738NGX/RinaChanBoard/Documents/Assets/头图.png

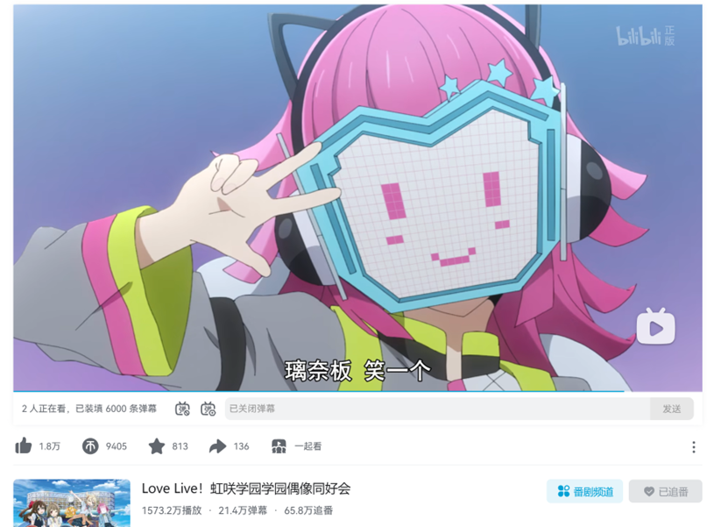
Documents/Assets/头图.png
