738NGX/RinaChanBoard/RinaChanBoardHardware/PCB/RinaBoard/resources/rina2.png

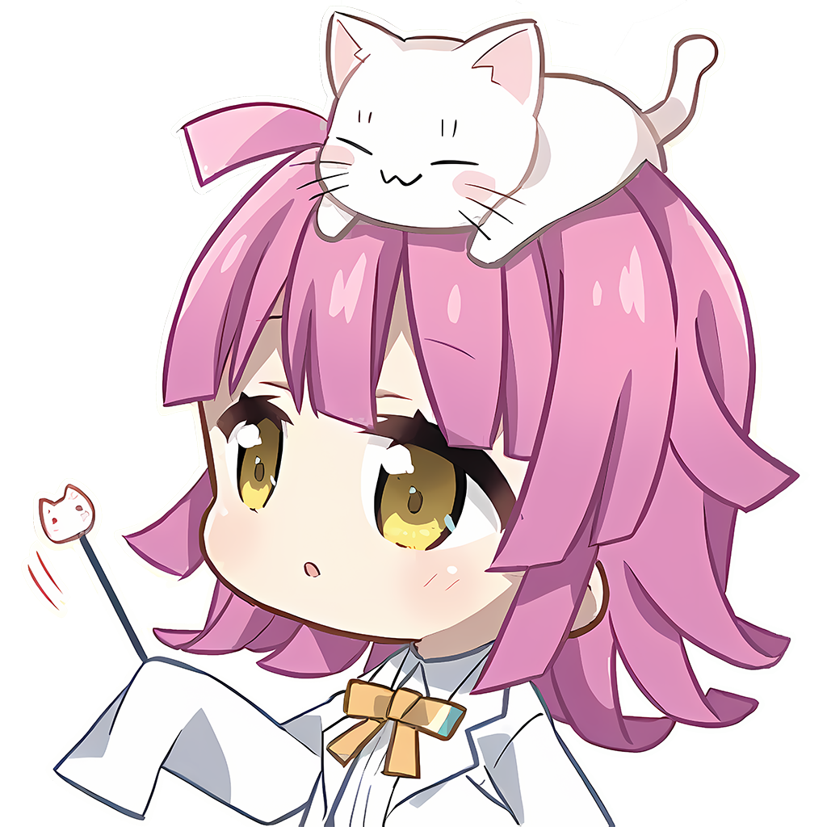
RinaChanBoardHardware/PCB/RinaBoard/resources/rina2.png
