738NGX/RinaChanBoard/RinaChanBoardHardware/PCB/RinaBoard/resources/rina3.png

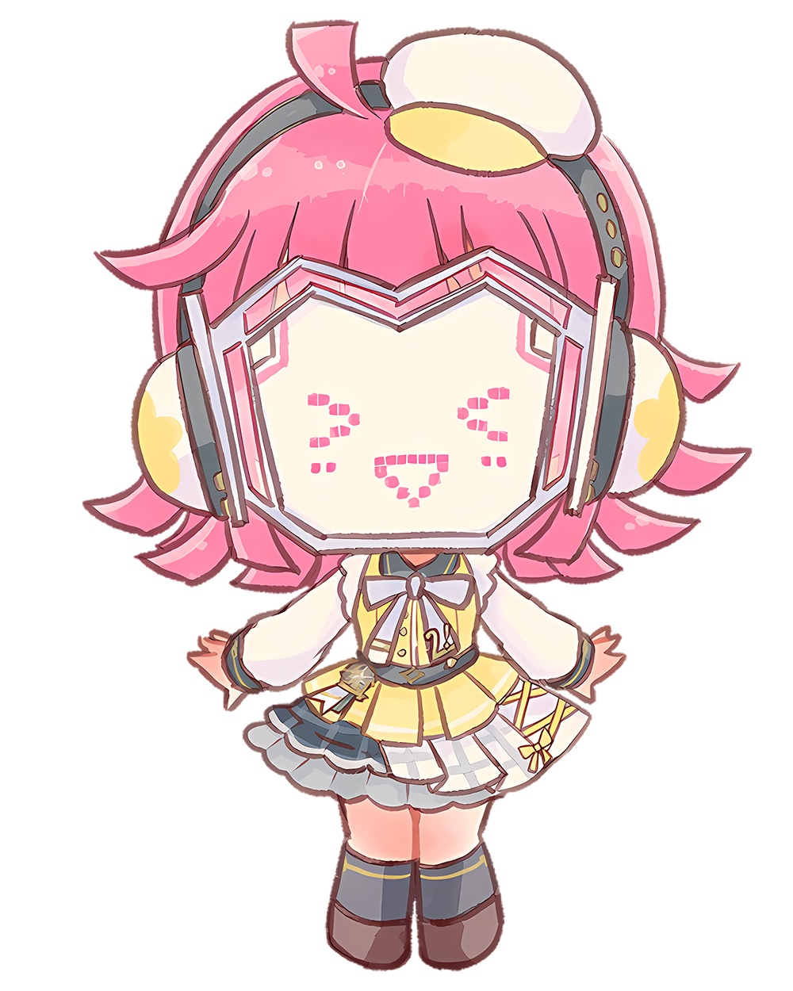
RinaChanBoardHardware/PCB/RinaBoard/resources/rina3.png
