738NGX/RinaChanBoard/RinaChanBoardHardware/PCB/RinaBoard/resources/rina.png

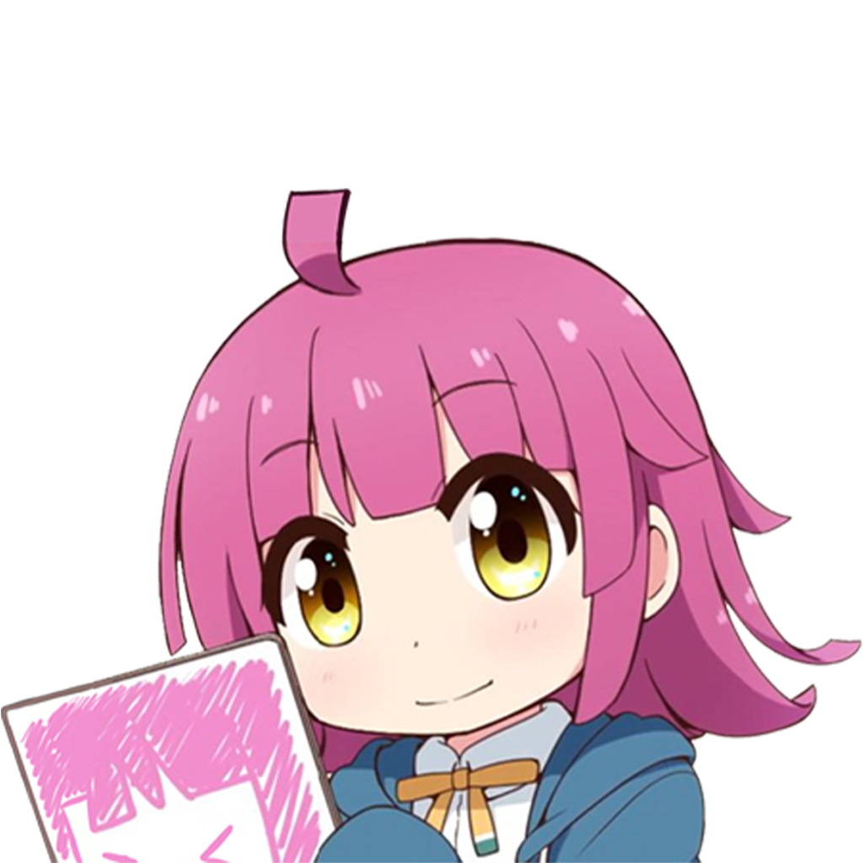
RinaChanBoardHardware/PCB/RinaBoard/resources/rina.png
