738NGX/RinaChanBoard/RinaChanBoardOperationCenter.wechatapp/images/cheek/01.png

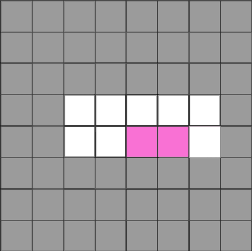
RinaChanBoardOperationCenter.wechatapp/images/cheek/01.png
