738NGX/RinaChanBoard/RinaChanBoardOperationCenter.wechatapp/images/cheek/03.png

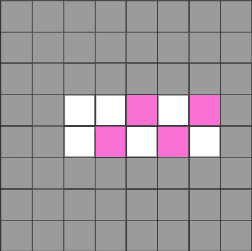
RinaChanBoardOperationCenter.wechatapp/images/cheek/03.png
