738NGX/RinaChanBoard/RinaChanBoardOperationCenter.wechatapp/images/cheek/04.png

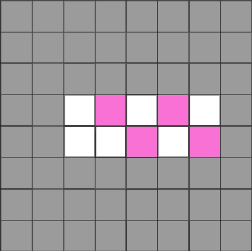
RinaChanBoardOperationCenter.wechatapp/images/cheek/04.png
