738NGX/RinaChanBoard/RinaChanBoardOperationCenter.wechatapp/images/connected.png

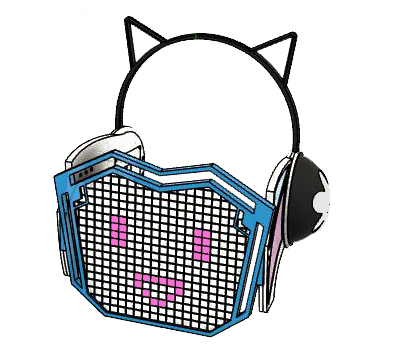
RinaChanBoardOperationCenter.wechatapp/images/connected.png
