738NGX/RinaChanBoard/RinaChanBoardOperationCenter.wechatapp/images/disconnected.png

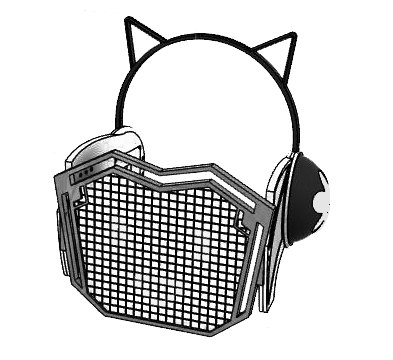
RinaChanBoardOperationCenter.wechatapp/images/disconnected.png
