738NGX/RinaChanBoard/RinaChanBoardOperationCenter.wechatapp/images/leye/05.png

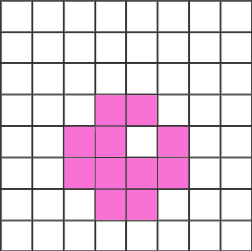
RinaChanBoardOperationCenter.wechatapp/images/leye/05.png
