738NGX/RinaChanBoard/RinaChanBoardOperationCenter.wechatapp/images/leye/09.png

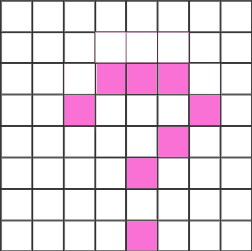
RinaChanBoardOperationCenter.wechatapp/images/leye/09.png
