738NGX/RinaChanBoard/RinaChanBoardOperationCenter.wechatapp/images/leye/18.png

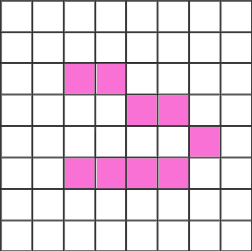
RinaChanBoardOperationCenter.wechatapp/images/leye/18.png
