738NGX/RinaChanBoard/RinaChanBoardOperationCenter.wechatapp/images/play.png

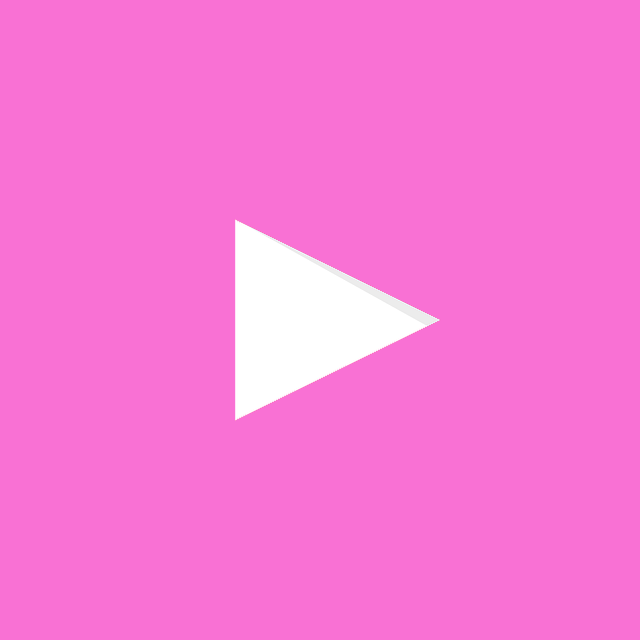
RinaChanBoardOperationCenter.wechatapp/images/play.png
