738NGX/RinaChanBoard/RinaChanBoardOperationCenter.wechatapp/images/reye/18.png

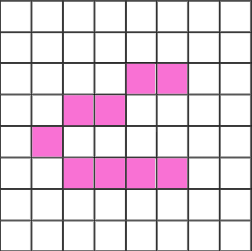
RinaChanBoardOperationCenter.wechatapp/images/reye/18.png
