738NGX/RinaChanBoard/RinaChanBoardOperationCenter/Assets/Resources/Image/FaceModule/000.png

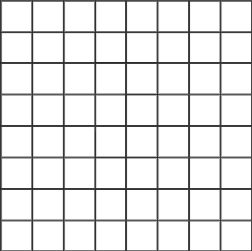
RinaChanBoardOperationCenter/Assets/Resources/Image/FaceModule/000.png
