738NGX/RinaChanBoard/RinaChanBoardOperationCenter/Assets/Resources/Image/FaceModule/101.png

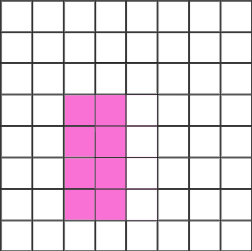
RinaChanBoardOperationCenter/Assets/Resources/Image/FaceModule/101.png
