738NGX/RinaChanBoard/RinaChanBoardOperationCenter/Assets/Resources/Image/FaceModule/103.png

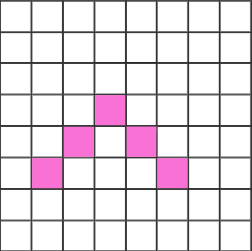
RinaChanBoardOperationCenter/Assets/Resources/Image/FaceModule/103.png
