738NGX/RinaChanBoard/RinaChanBoardOperationCenter/Assets/Resources/Image/FaceModule/104.png

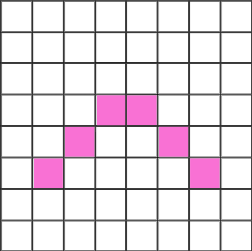
RinaChanBoardOperationCenter/Assets/Resources/Image/FaceModule/104.png
