738NGX/RinaChanBoard/RinaChanBoardOperationCenter/Assets/Resources/Image/FaceModule/105.png

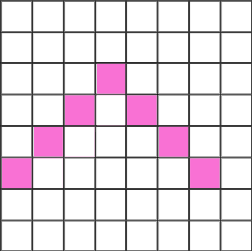
RinaChanBoardOperationCenter/Assets/Resources/Image/FaceModule/105.png
