738NGX/RinaChanBoard/RinaChanBoardOperationCenter/Assets/Resources/Image/FaceModule/106.png

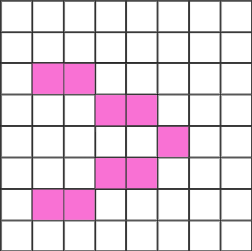
RinaChanBoardOperationCenter/Assets/Resources/Image/FaceModule/106.png
