738NGX/RinaChanBoard/RinaChanBoardOperationCenter/Assets/Resources/Image/FaceModule/107.png

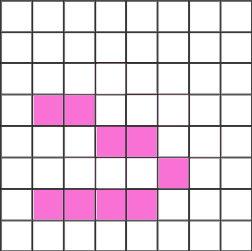
RinaChanBoardOperationCenter/Assets/Resources/Image/FaceModule/107.png
