738NGX/RinaChanBoard/RinaChanBoardOperationCenter/Assets/Resources/Image/FaceModule/109.png

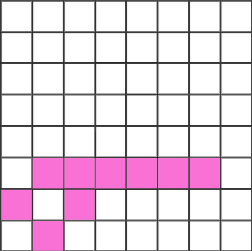
RinaChanBoardOperationCenter/Assets/Resources/Image/FaceModule/109.png
