738NGX/RinaChanBoard/RinaChanBoardOperationCenter/Assets/Resources/Image/FaceModule/110.png

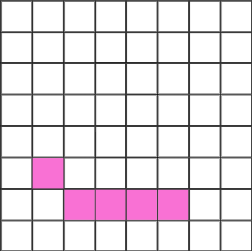
RinaChanBoardOperationCenter/Assets/Resources/Image/FaceModule/110.png
