738NGX/RinaChanBoard/RinaChanBoardOperationCenter/Assets/Resources/Image/FaceModule/111.png

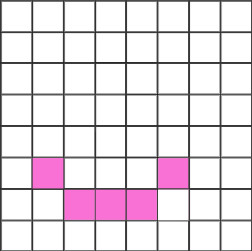
RinaChanBoardOperationCenter/Assets/Resources/Image/FaceModule/111.png
