738NGX/RinaChanBoard/RinaChanBoardOperationCenter/Assets/Resources/Image/FaceModule/112.png

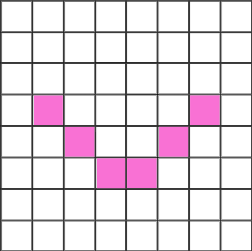
RinaChanBoardOperationCenter/Assets/Resources/Image/FaceModule/112.png
