738NGX/RinaChanBoard/RinaChanBoardOperationCenter/Assets/Resources/Image/FaceModule/113.png

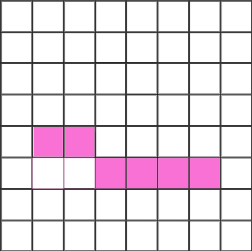
RinaChanBoardOperationCenter/Assets/Resources/Image/FaceModule/113.png
