738NGX/RinaChanBoard/RinaChanBoardOperationCenter/Assets/Resources/Image/FaceModule/117.png

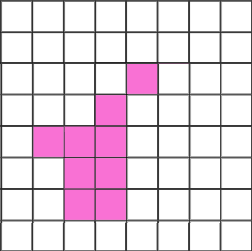
RinaChanBoardOperationCenter/Assets/Resources/Image/FaceModule/117.png
