738NGX/RinaChanBoard/RinaChanBoardOperationCenter/Assets/Resources/Image/FaceModule/118.png

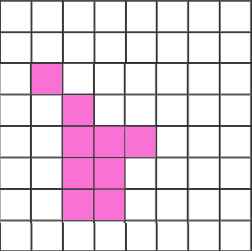
RinaChanBoardOperationCenter/Assets/Resources/Image/FaceModule/118.png
