738NGX/RinaChanBoard/RinaChanBoardOperationCenter/Assets/Resources/Image/FaceModule/119.png

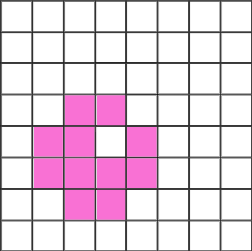
RinaChanBoardOperationCenter/Assets/Resources/Image/FaceModule/119.png
