738NGX/RinaChanBoard/RinaChanBoardOperationCenter/Assets/Resources/Image/FaceModule/122.png

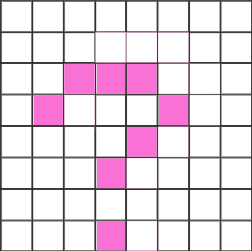
RinaChanBoardOperationCenter/Assets/Resources/Image/FaceModule/122.png
