738NGX/RinaChanBoard/RinaChanBoardOperationCenter/Assets/Resources/Image/FaceModule/123.png

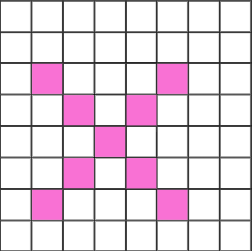
RinaChanBoardOperationCenter/Assets/Resources/Image/FaceModule/123.png
