738NGX/RinaChanBoard/RinaChanBoardOperationCenter/Assets/Resources/Image/FaceModule/124.png

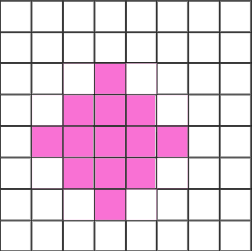
RinaChanBoardOperationCenter/Assets/Resources/Image/FaceModule/124.png
