738NGX/RinaChanBoard/RinaChanBoardOperationCenter/Assets/Resources/Image/FaceModule/125.png

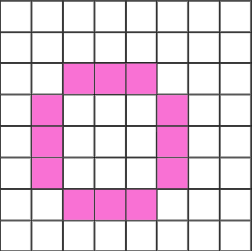
RinaChanBoardOperationCenter/Assets/Resources/Image/FaceModule/125.png
