738NGX/RinaChanBoard/RinaChanBoardOperationCenter/Assets/Resources/Image/FaceModule/126.png

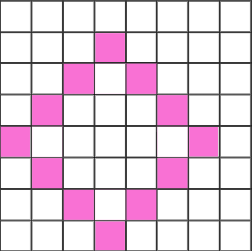
RinaChanBoardOperationCenter/Assets/Resources/Image/FaceModule/126.png
