738NGX/RinaChanBoard/RinaChanBoardOperationCenter/Assets/Resources/Image/FaceModule/127.png

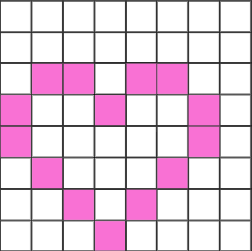
RinaChanBoardOperationCenter/Assets/Resources/Image/FaceModule/127.png
