738NGX/RinaChanBoard/RinaChanBoardOperationCenter/Assets/Resources/Image/FaceModule/201.png

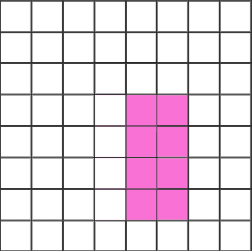
RinaChanBoardOperationCenter/Assets/Resources/Image/FaceModule/201.png
