738NGX/RinaChanBoard/RinaChanBoardOperationCenter/Assets/Resources/Image/FaceModule/203.png

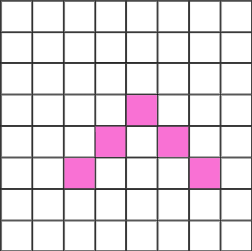
RinaChanBoardOperationCenter/Assets/Resources/Image/FaceModule/203.png
