738NGX/RinaChanBoard/RinaChanBoardOperationCenter/Assets/Resources/Image/FaceModule/205.png

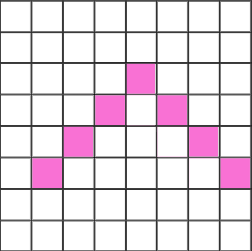
RinaChanBoardOperationCenter/Assets/Resources/Image/FaceModule/205.png
