738NGX/RinaChanBoard/RinaChanBoardOperationCenter/Assets/Resources/Image/FaceModule/206.png

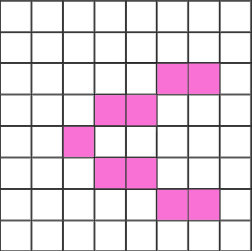
RinaChanBoardOperationCenter/Assets/Resources/Image/FaceModule/206.png
