738NGX/RinaChanBoard/RinaChanBoardOperationCenter/Assets/Resources/Image/FaceModule/207.png

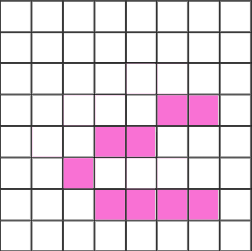
RinaChanBoardOperationCenter/Assets/Resources/Image/FaceModule/207.png
