738NGX/RinaChanBoard/RinaChanBoardOperationCenter/Assets/Resources/Image/FaceModule/209.png

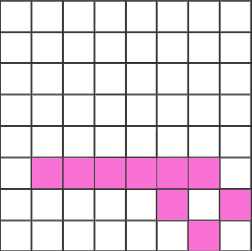
RinaChanBoardOperationCenter/Assets/Resources/Image/FaceModule/209.png
