738NGX/RinaChanBoard/RinaChanBoardOperationCenter/Assets/Resources/Image/FaceModule/210.png

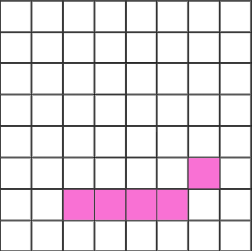
RinaChanBoardOperationCenter/Assets/Resources/Image/FaceModule/210.png
