738NGX/RinaChanBoard/RinaChanBoardOperationCenter/Assets/Resources/Image/FaceModule/211.png

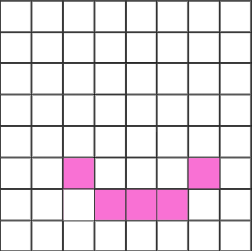
RinaChanBoardOperationCenter/Assets/Resources/Image/FaceModule/211.png
