738NGX/RinaChanBoard/RinaChanBoardOperationCenter/Assets/Resources/Image/FaceModule/213.png

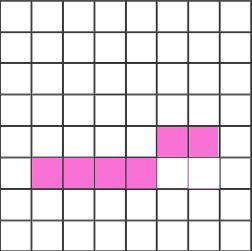
RinaChanBoardOperationCenter/Assets/Resources/Image/FaceModule/213.png
