738NGX/RinaChanBoard/RinaChanBoardOperationCenter/Assets/Resources/Image/FaceModule/214.png

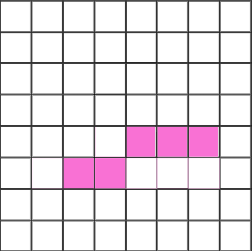
RinaChanBoardOperationCenter/Assets/Resources/Image/FaceModule/214.png
