738NGX/RinaChanBoard/RinaChanBoardOperationCenter/Assets/Resources/Image/FaceModule/216.png

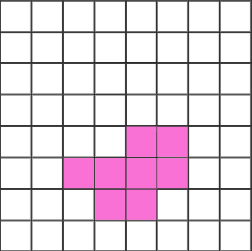
RinaChanBoardOperationCenter/Assets/Resources/Image/FaceModule/216.png
