738NGX/RinaChanBoard/RinaChanBoardOperationCenter/Assets/Resources/Image/FaceModule/217.png

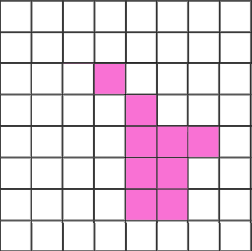
RinaChanBoardOperationCenter/Assets/Resources/Image/FaceModule/217.png
