738NGX/RinaChanBoard/RinaChanBoardOperationCenter/Assets/Resources/Image/FaceModule/218.png

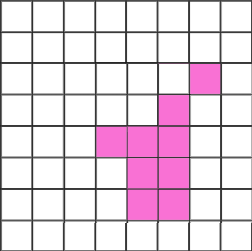
RinaChanBoardOperationCenter/Assets/Resources/Image/FaceModule/218.png
