738NGX/RinaChanBoard/RinaChanBoardOperationCenter/Assets/Resources/Image/FaceModule/219.png

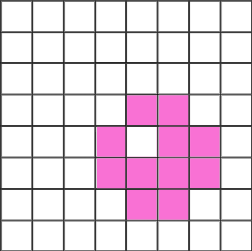
RinaChanBoardOperationCenter/Assets/Resources/Image/FaceModule/219.png
