738NGX/RinaChanBoard/RinaChanBoardOperationCenter/Assets/Resources/Image/FaceModule/222.png

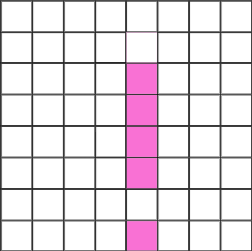
RinaChanBoardOperationCenter/Assets/Resources/Image/FaceModule/222.png
