738NGX/RinaChanBoard/RinaChanBoardOperationCenter/Assets/Resources/Image/FaceModule/223.png

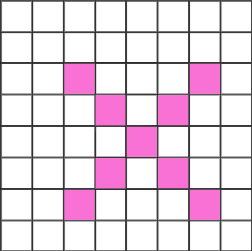
RinaChanBoardOperationCenter/Assets/Resources/Image/FaceModule/223.png
