738NGX/RinaChanBoard/RinaChanBoardOperationCenter/Assets/Resources/Image/FaceModule/224.png

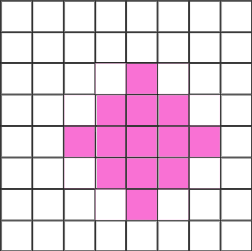
RinaChanBoardOperationCenter/Assets/Resources/Image/FaceModule/224.png
