738NGX/RinaChanBoard/RinaChanBoardOperationCenter/Assets/Resources/Image/FaceModule/225.png

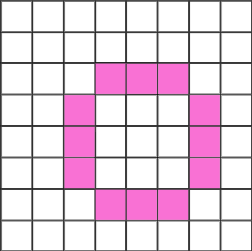
RinaChanBoardOperationCenter/Assets/Resources/Image/FaceModule/225.png
