738NGX/RinaChanBoard/RinaChanBoardOperationCenter/Assets/Resources/Image/FaceModule/226.png

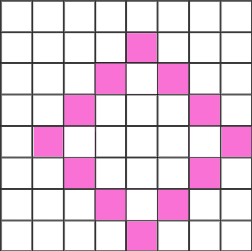
RinaChanBoardOperationCenter/Assets/Resources/Image/FaceModule/226.png
