738NGX/RinaChanBoard/RinaChanBoardOperationCenter/Assets/Resources/Image/FaceModule/227.png

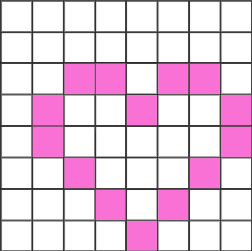
RinaChanBoardOperationCenter/Assets/Resources/Image/FaceModule/227.png
