738NGX/RinaChanBoard/RinaChanBoardOperationCenter/Assets/Resources/Image/FaceModule/302.png

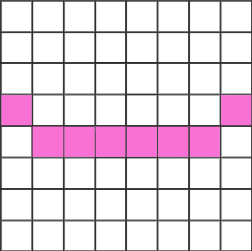
RinaChanBoardOperationCenter/Assets/Resources/Image/FaceModule/302.png
