738NGX/RinaChanBoard/RinaChanBoardOperationCenter/Assets/Resources/Image/FaceModule/303.png

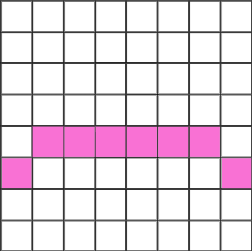
RinaChanBoardOperationCenter/Assets/Resources/Image/FaceModule/303.png
