738NGX/RinaChanBoard/RinaChanBoardOperationCenter/Assets/Resources/Image/FaceModule/304.png

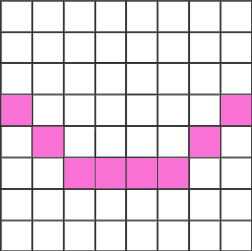
RinaChanBoardOperationCenter/Assets/Resources/Image/FaceModule/304.png
