738NGX/RinaChanBoard/RinaChanBoardOperationCenter/Assets/Resources/Image/FaceModule/305.png

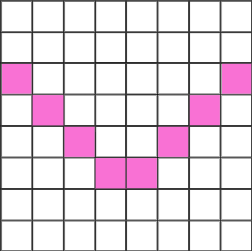
RinaChanBoardOperationCenter/Assets/Resources/Image/FaceModule/305.png
