738NGX/RinaChanBoard/RinaChanBoardOperationCenter/Assets/Resources/Image/FaceModule/307.png

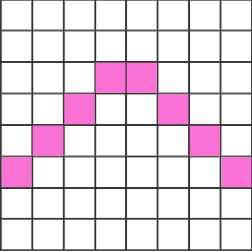
RinaChanBoardOperationCenter/Assets/Resources/Image/FaceModule/307.png
