738NGX/RinaChanBoard/RinaChanBoardOperationCenter/Assets/Resources/Image/FaceModule/308.png

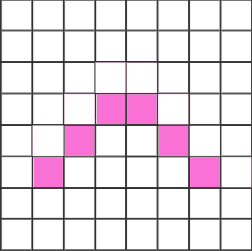
RinaChanBoardOperationCenter/Assets/Resources/Image/FaceModule/308.png
