738NGX/RinaChanBoard/RinaChanBoardOperationCenter/Assets/Resources/Image/FaceModule/309.png

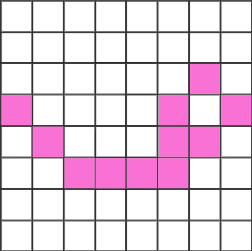
RinaChanBoardOperationCenter/Assets/Resources/Image/FaceModule/309.png
