738NGX/RinaChanBoard/RinaChanBoardOperationCenter/Assets/Resources/Image/FaceModule/310.png

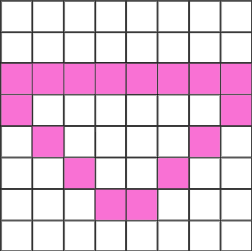
RinaChanBoardOperationCenter/Assets/Resources/Image/FaceModule/310.png
