738NGX/RinaChanBoard/RinaChanBoardOperationCenter/Assets/Resources/Image/FaceModule/311.png

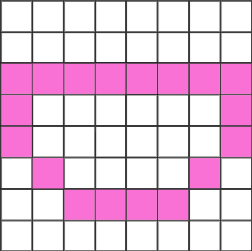
RinaChanBoardOperationCenter/Assets/Resources/Image/FaceModule/311.png
