738NGX/RinaChanBoard/RinaChanBoardOperationCenter/Assets/Resources/Image/FaceModule/312.png

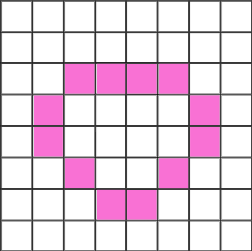
RinaChanBoardOperationCenter/Assets/Resources/Image/FaceModule/312.png
