738NGX/RinaChanBoard/RinaChanBoardOperationCenter/Assets/Resources/Image/FaceModule/314.png

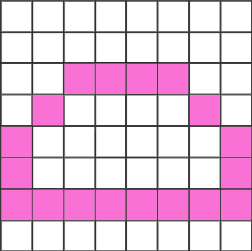
RinaChanBoardOperationCenter/Assets/Resources/Image/FaceModule/314.png
