738NGX/RinaChanBoard/RinaChanBoardOperationCenter/Assets/Resources/Image/FaceModule/315.png

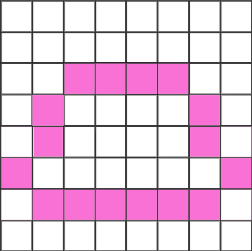
RinaChanBoardOperationCenter/Assets/Resources/Image/FaceModule/315.png
