738NGX/RinaChanBoard/RinaChanBoardOperationCenter/Assets/Resources/Image/FaceModule/316.png

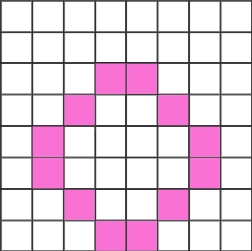
RinaChanBoardOperationCenter/Assets/Resources/Image/FaceModule/316.png
