738NGX/RinaChanBoard/RinaChanBoardOperationCenter/Assets/Resources/Image/FaceModule/317.png

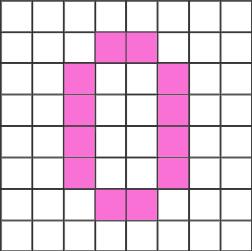
RinaChanBoardOperationCenter/Assets/Resources/Image/FaceModule/317.png
