738NGX/RinaChanBoard/RinaChanBoardOperationCenter/Assets/Resources/Image/FaceModule/318.png

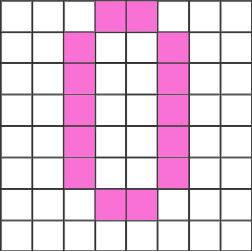
RinaChanBoardOperationCenter/Assets/Resources/Image/FaceModule/318.png
