738NGX/RinaChanBoard/RinaChanBoardOperationCenter/Assets/Resources/Image/FaceModule/319.png

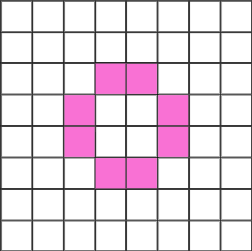
RinaChanBoardOperationCenter/Assets/Resources/Image/FaceModule/319.png
