738NGX/RinaChanBoard/RinaChanBoardOperationCenter/Assets/Resources/Image/FaceModule/320.png

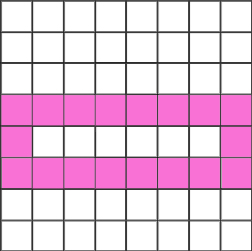
RinaChanBoardOperationCenter/Assets/Resources/Image/FaceModule/320.png
