738NGX/RinaChanBoard/RinaChanBoardOperationCenter/Assets/Resources/Image/FaceModule/323.png

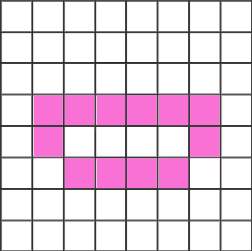
RinaChanBoardOperationCenter/Assets/Resources/Image/FaceModule/323.png
