738NGX/RinaChanBoard/RinaChanBoardOperationCenter/Assets/Resources/Image/FaceModule/324.png

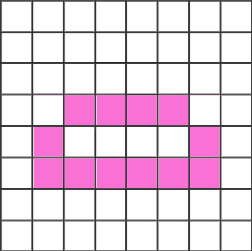
RinaChanBoardOperationCenter/Assets/Resources/Image/FaceModule/324.png
