738NGX/RinaChanBoard/RinaChanBoardOperationCenter/Assets/Resources/Image/FaceModule/326.png

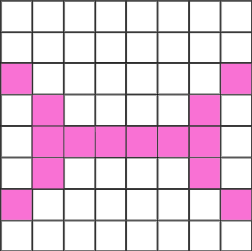
RinaChanBoardOperationCenter/Assets/Resources/Image/FaceModule/326.png
