738NGX/RinaChanBoard/RinaChanBoardOperationCenter/Assets/Resources/Image/FaceModule/327.png

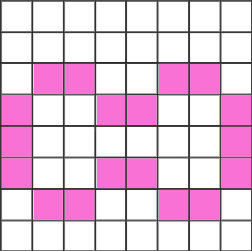
RinaChanBoardOperationCenter/Assets/Resources/Image/FaceModule/327.png
