738NGX/RinaChanBoard/RinaChanBoardOperationCenter/Assets/Resources/Image/FaceModule/328.png

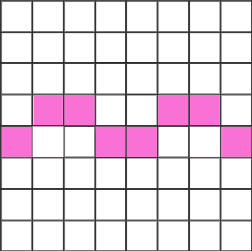
RinaChanBoardOperationCenter/Assets/Resources/Image/FaceModule/328.png
