738NGX/RinaChanBoard/RinaChanBoardOperationCenter/Assets/Resources/Image/FaceModule/330.png

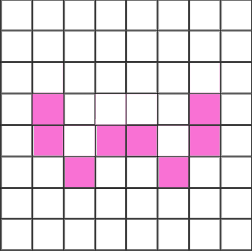
RinaChanBoardOperationCenter/Assets/Resources/Image/FaceModule/330.png
