738NGX/RinaChanBoard/RinaChanBoardOperationCenter/Assets/Resources/Image/FaceModule/331.png

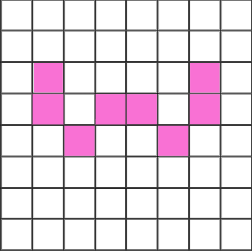
RinaChanBoardOperationCenter/Assets/Resources/Image/FaceModule/331.png
