738NGX/RinaChanBoard/RinaChanBoardOperationCenter/Assets/Resources/Image/FaceModule/332.png

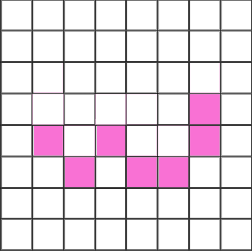
RinaChanBoardOperationCenter/Assets/Resources/Image/FaceModule/332.png
