738NGX/RinaChanBoard/RinaChanBoardOperationCenter/Assets/Resources/Image/FaceModule/400.png

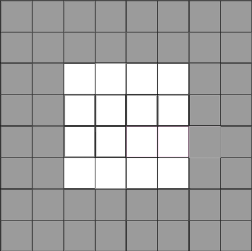
RinaChanBoardOperationCenter/Assets/Resources/Image/FaceModule/400.png
