738NGX/RinaChanBoard/RinaChanBoardOperationCenter/Assets/Resources/Image/FaceModule/403.png

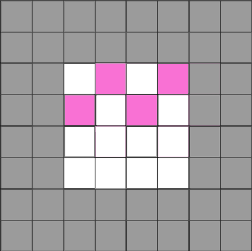
RinaChanBoardOperationCenter/Assets/Resources/Image/FaceModule/403.png
