738NGX/RinaChanBoard/RinaChanBoardOperationCenter/Assets/Resources/Image/FaceModule/404.png

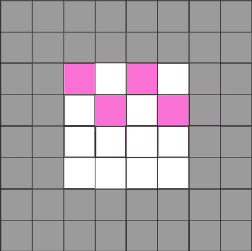
RinaChanBoardOperationCenter/Assets/Resources/Image/FaceModule/404.png
