738NGX/RinaChanBoard/RinaChanBoardOperationCenter/Assets/Resources/Image/Music/music_lumf.png

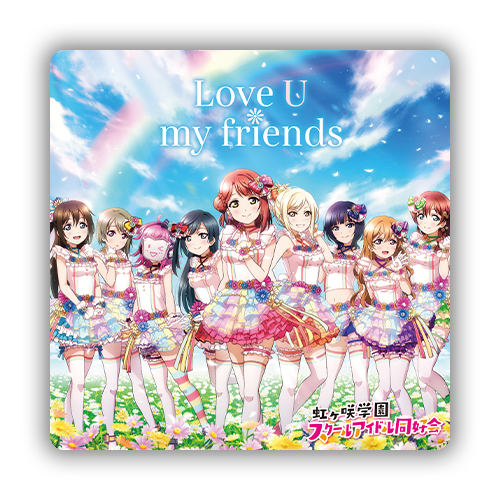
RinaChanBoardOperationCenter/Assets/Resources/Image/Music/music_lumf.png
