738NGX/RinaChanBoard/RinaChanBoardOperationCenter/Assets/Resources/Image/Music/music_solo0.png

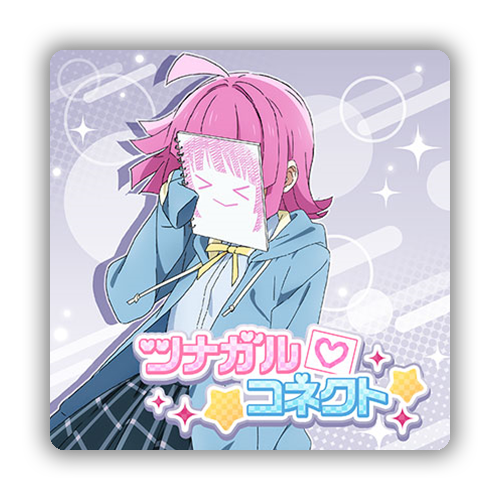
RinaChanBoardOperationCenter/Assets/Resources/Image/Music/music_solo0.png
