738NGX/RinaChanBoard/RinaChanBoardOperationCenter/Assets/Resources/Image/Music/music_solo1.png

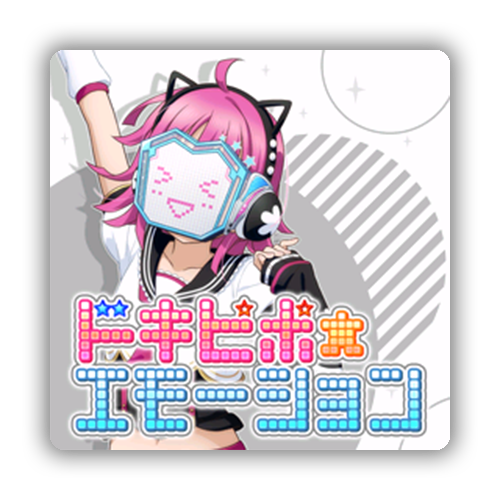
RinaChanBoardOperationCenter/Assets/Resources/Image/Music/music_solo1.png
