738NGX/RinaChanBoard/RinaChanBoardOperationCenter/Assets/Resources/Image/Music/music_solo2.png

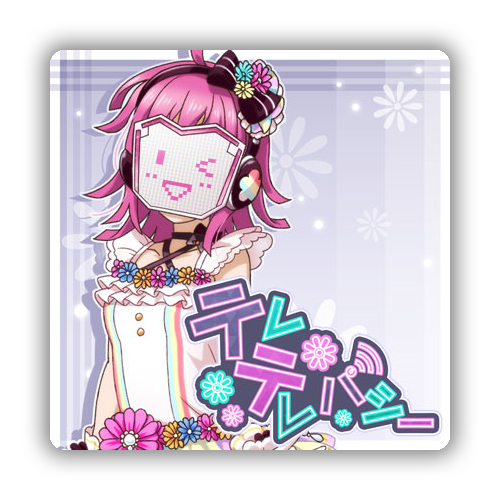
RinaChanBoardOperationCenter/Assets/Resources/Image/Music/music_solo2.png
