738NGX/RinaChanBoard/RinaChanBoardOperationCenter/Assets/Resources/Image/Music/music_solo3.png

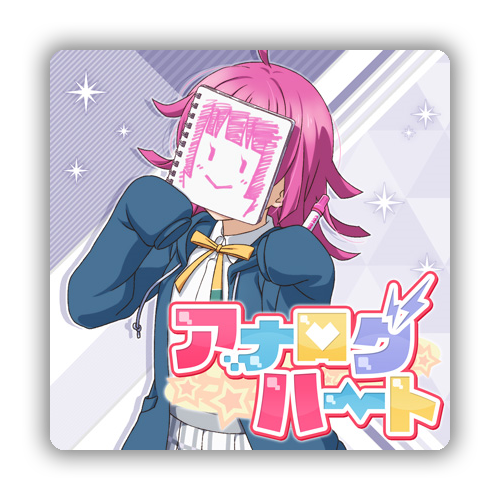
RinaChanBoardOperationCenter/Assets/Resources/Image/Music/music_solo3.png
