738NGX/RinaChanBoard/RinaChanBoardOperationCenter/Assets/Resources/Image/Music/music_solo4.png

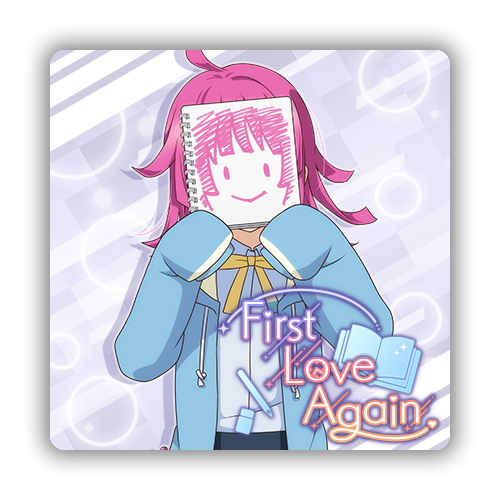
RinaChanBoardOperationCenter/Assets/Resources/Image/Music/music_solo4.png
