738NGX/RinaChanBoard/RinaChanBoardOperationCenter/Assets/Resources/Image/Music/music_solo5.png

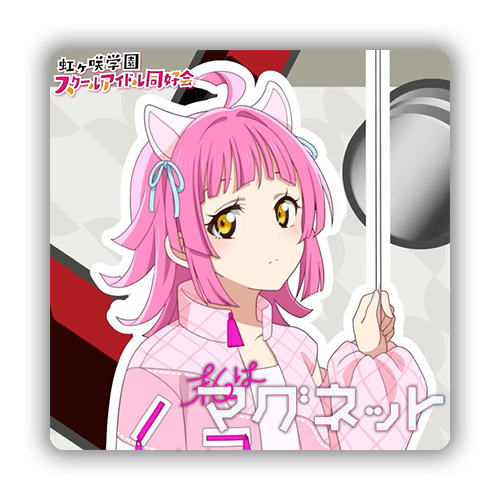
RinaChanBoardOperationCenter/Assets/Resources/Image/Music/music_solo5.png
