738NGX/RinaChanBoard/RinaChanBoardOperationCenter/Assets/Resources/Image/Music/music_tkmk.png

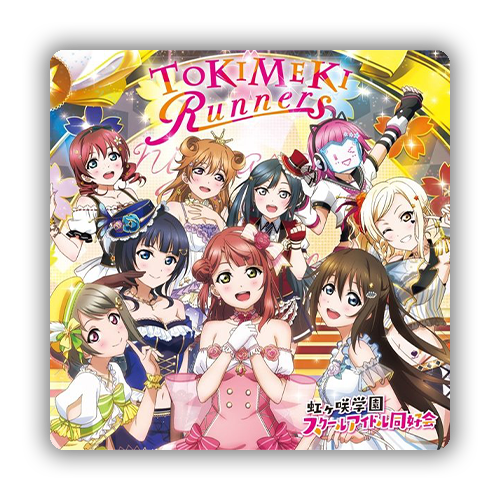
RinaChanBoardOperationCenter/Assets/Resources/Image/Music/music_tkmk.png
