738NGX/RinaChanBoard/RinaChanBoardOperationCenter/Assets/Resources/Image/Rina/rina-01-c.png

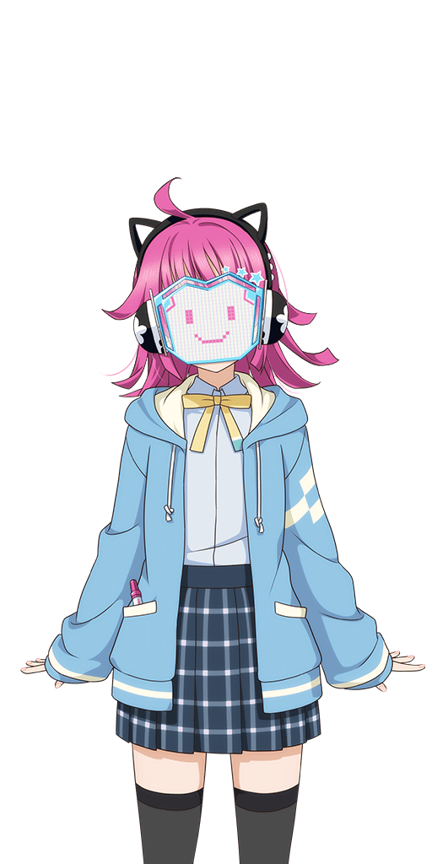
RinaChanBoardOperationCenter/Assets/Resources/Image/Rina/rina-01-c.png
