738NGX/RinaChanBoard/RinaChanBoardOperationCenter/Assets/Resources/Image/Rina/rina-06-c.png

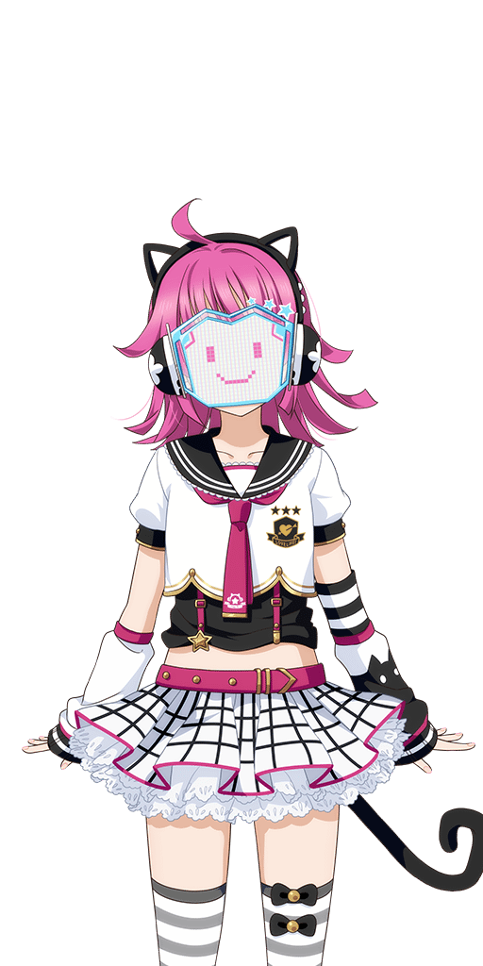
RinaChanBoardOperationCenter/Assets/Resources/Image/Rina/rina-06-c.png
