738NGX/RinaChanBoard/RinaChanBoardTester/assets/frame.png

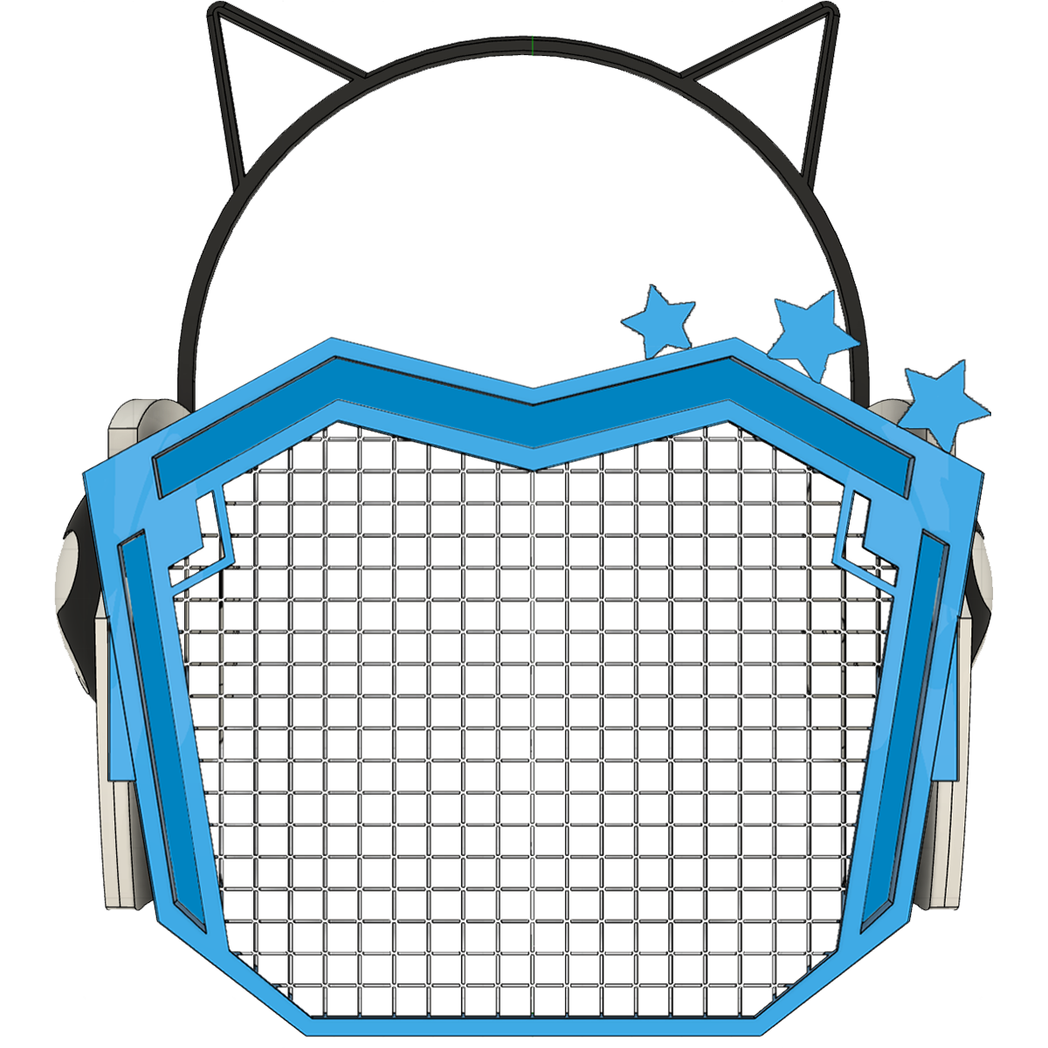
RinaChanBoardTester/assets/frame.png
