738NGX/RinaChanBoard/RinaChanBoardHardware/RinaChanBoardHardware/include/led.h

#pragma once
#include <Arduino.h>
#include <FastLED.h>
#include <cstdint>

#define NUM_LEDS    256
#define DATA_PIN    D1
#define LED_MAX_ROW 16
#define LED_MAX_COL 18
#define LED_TYPE    WS2812
#define COLOR_ORDER GRB

/**
 * @brief led灯初始化
 *
 * @param leds
 * @param color
 */
void initLED(CRGB leds[], CRGB color);

/**
 * @brief 表情Hex字节流解码
 *
 * @param[in]   hexBytes  Hex字节流
 * @param[out]  cells     解码后的表情矩阵
 * @param[in]   length    字节流长度

 */
void decodeFaceHex(const char hexBytes[],
                   const uint8_t offsetRows,
                   uint8_t (&cells)[LED_MAX_ROW][LED_MAX_COL],
                   size_t length);

/**
 * @brief 通过RGB值直接更新led颜色
 *
 * @param color_code
 * @param leds
 */
void updateColor(CRGB leds[],
                 const uint8_t &R,
                 const uint8_t &G,
                 const uint8_t &B);

/**
 * @brief 使用HexString更新led颜色，不要用于传输
 *
 * @param color_code
 * @param leds
 */
[[deprecated]] void updateColor(String color_code,
                                CRGB leds[],
                                uint8_t &R,
                                uint8_t &G,
                                uint8_t &B);

/**
 * @brief 从数组更新璃奈板表情
 *
 * @param[in]  face 16*18的数组
 * @param[out] leds 目标led
 * @param[in]  color 目标颜色
 */
void faceUpdate_FullPack(uint8_t face[16][18],
                         CRGB leds[],
                         CRGB color);

/**
 * @brief
 *
 * @param[in]   LEyeCode   左眼表情编号
 * @param[in]   REyeCode   右眼表情编号
 * @param[in]   MouthCode  嘴巴表情编号
 * @param[in]   cheekCode  脸颊表情编号
 * @param[out]  leds       目标led矩阵
 * @param[in]   color      目标颜色
 */
void faceUpdate_litePackage(uint8_t const LEyeCode,
                            uint8_t const REyeCode,
                            uint8_t const MouthCode,
                            uint8_t const cheekCode,
                            CRGB leds[],
                            CRGB color);

/**
 * @brief 从状态字符串更新璃奈板表情
 * @warning 注意：不要用于UDP传输
 * @param[in]   hexString   72位长的十六进制状态字符串,可以被译码位16*18的数组
 * @param[out]  leds        目标led
 * @param[in]   color       目标颜色
 */
void faceUpdate_StringFullPack(const String hexString,
                               CRGB leds[],
                               CRGB color);

/**
 * @brief 从led开闭状态获取状态字符串
 *
 * @param leds 源led
 * @return String 状态字符串
 */
void getFaceHex(CRGB leds[], uint8_t *hexData);
